sdylewski/MajorHack-Stealthchanger/Nudge Sexbolt Bed Top Mount/Images/bracket_2020mount1.jpg

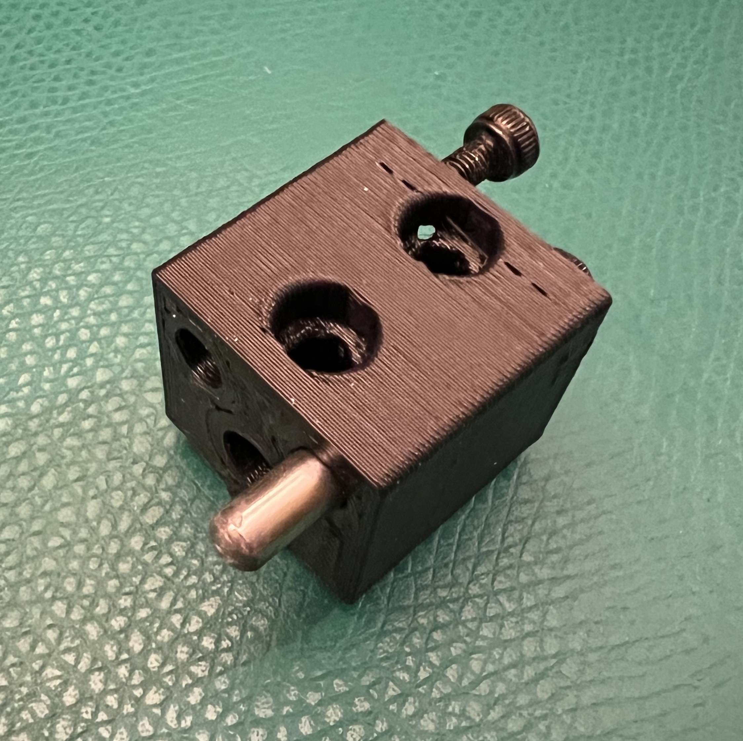
Nudge Sexbolt Bed Top Mount/Images/bracket_2020mount1.jpg
