sdylewski/MajorHack-Stealthchanger/Nudge Sexbolt Bed Top Mount/Images/bracket_2020mount_tnuts.jpg

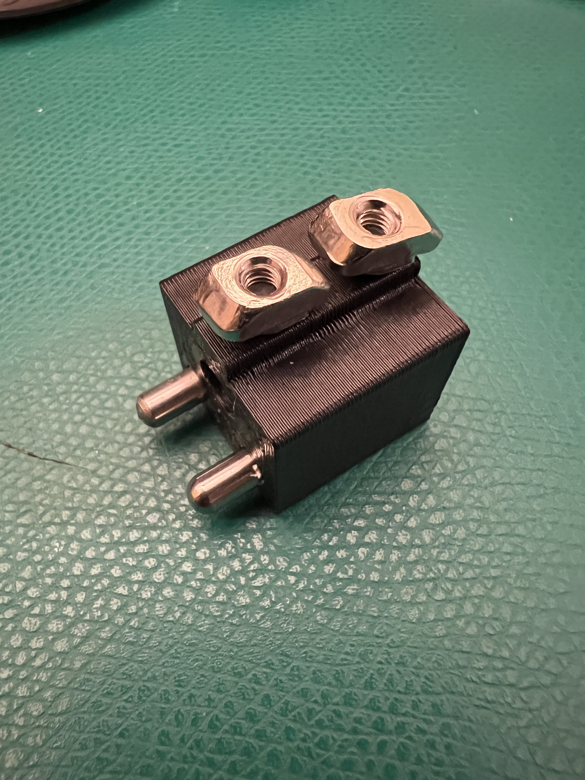
Nudge Sexbolt Bed Top Mount/Images/bracket_2020mount_tnuts.jpg
