sdylewski/MajorHack-Stealthchanger/Nudge Sexbolt Bed Top Mount/Images/bracket_block_heatset.jpg

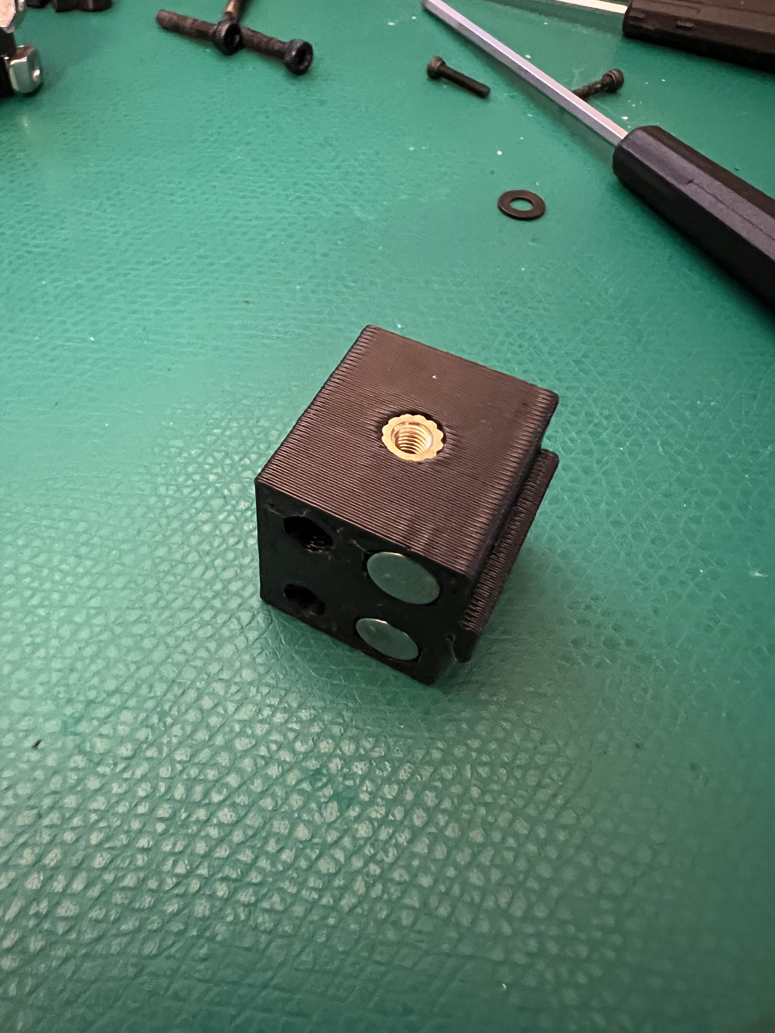
Nudge Sexbolt Bed Top Mount/Images/bracket_block_heatset.jpg
