sdylewski/MajorHack-Stealthchanger/Nudge Sexbolt Bed Top Mount/Images/bracket_magnets.jpg

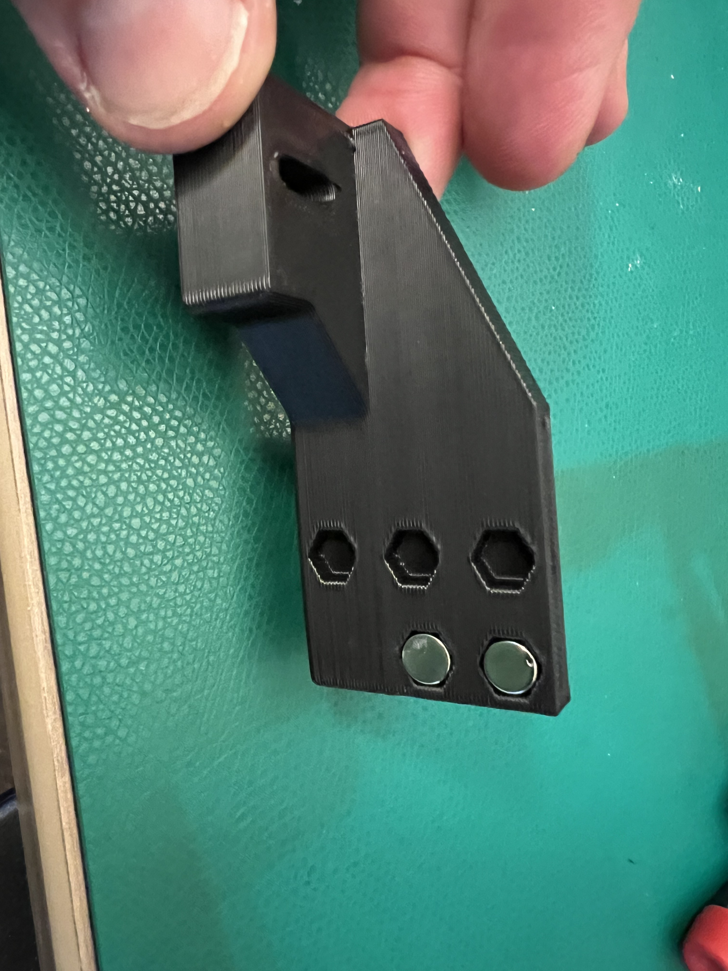
Nudge Sexbolt Bed Top Mount/Images/bracket_magnets.jpg
