sdylewski/MajorHack-Stealthchanger/Nudge Sexbolt Bed Top Mount/Images/bracket_rear_magnets.jpg

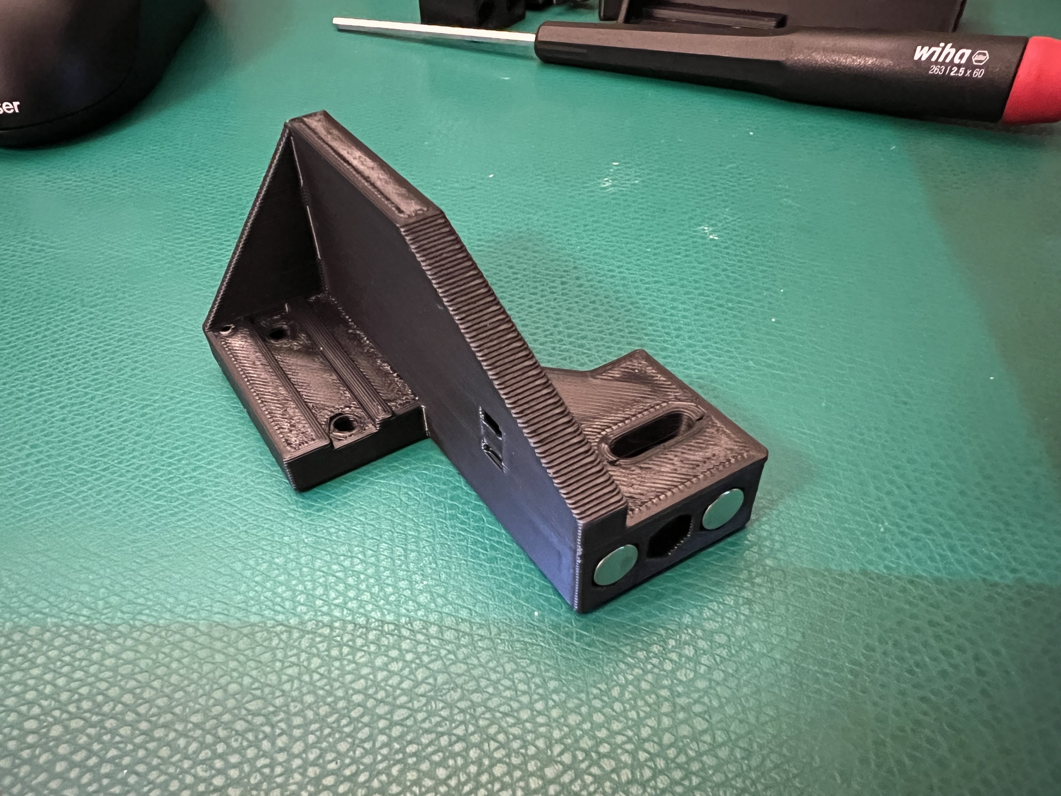
Nudge Sexbolt Bed Top Mount/Images/bracket_rear_magnets.jpg
