sdylewski/MajorHack-Stealthchanger/Nudge Sexbolt Bed Top Mount/Images/in_use.jpg

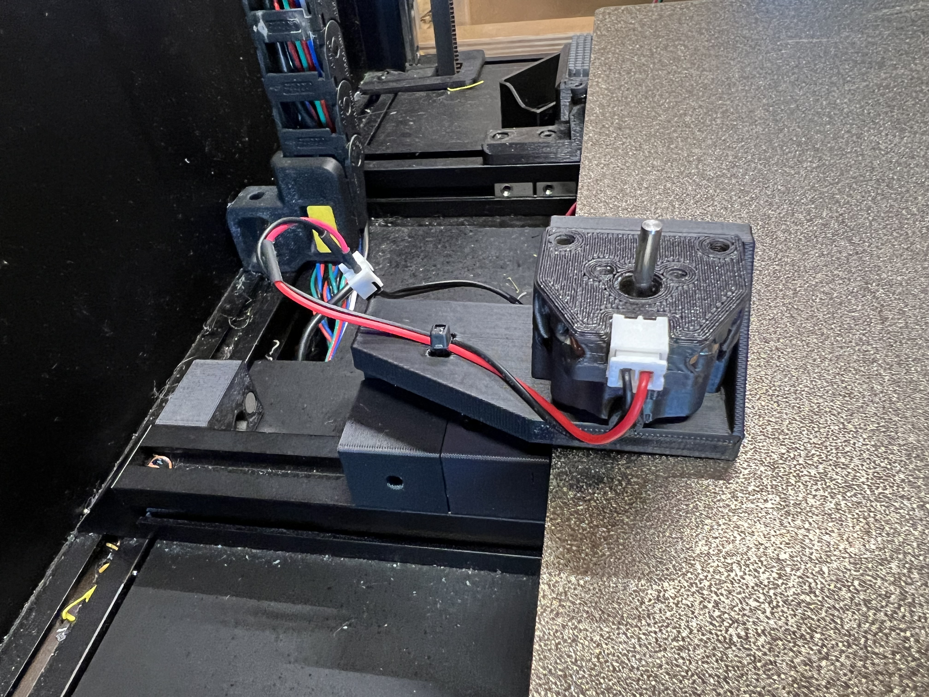
Nudge Sexbolt Bed Top Mount/Images/in_use.jpg
