sdylewski/MajorHack-Stealthchanger/Nudge Sexbolt Bed Top Mount/Images/in_use.png

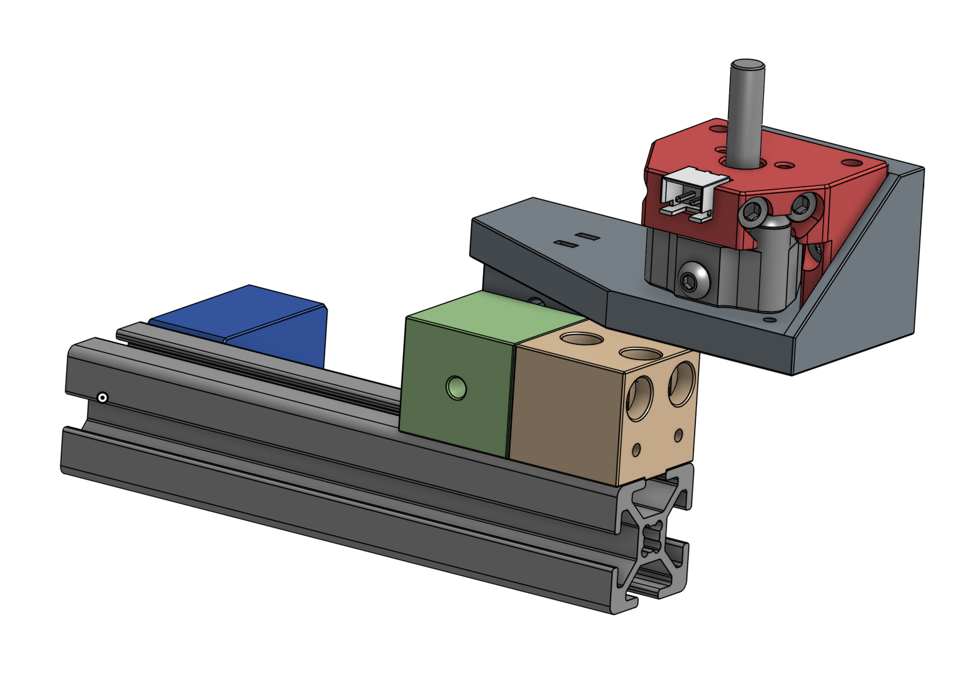
Nudge Sexbolt Bed Top Mount/Images/in_use.png
