sdylewski/MajorHack-Stealthchanger/Nudge Sexbolt Bed Top Mount/Images/rear dock magnets.jpg

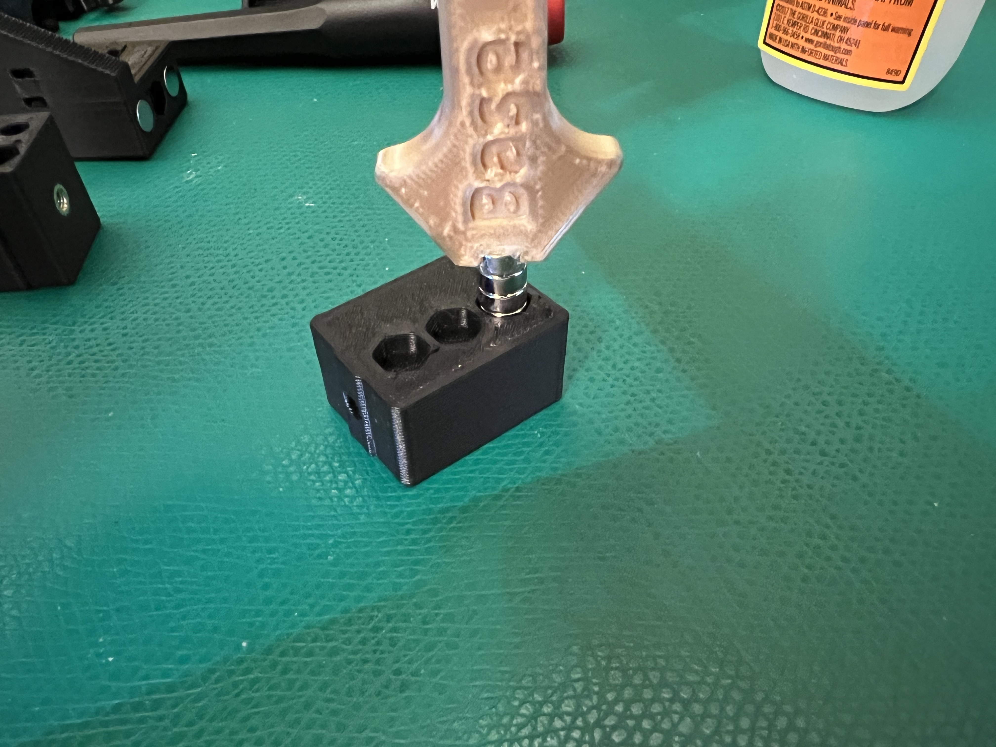
Nudge Sexbolt Bed Top Mount/Images/rear dock magnets.jpg
