sdylewski/MajorHack-Stealthchanger/Nudge Sexbolt Bed Top Mount/Images/Screenshot 2025-10-11 at 2.33.38 PM.png

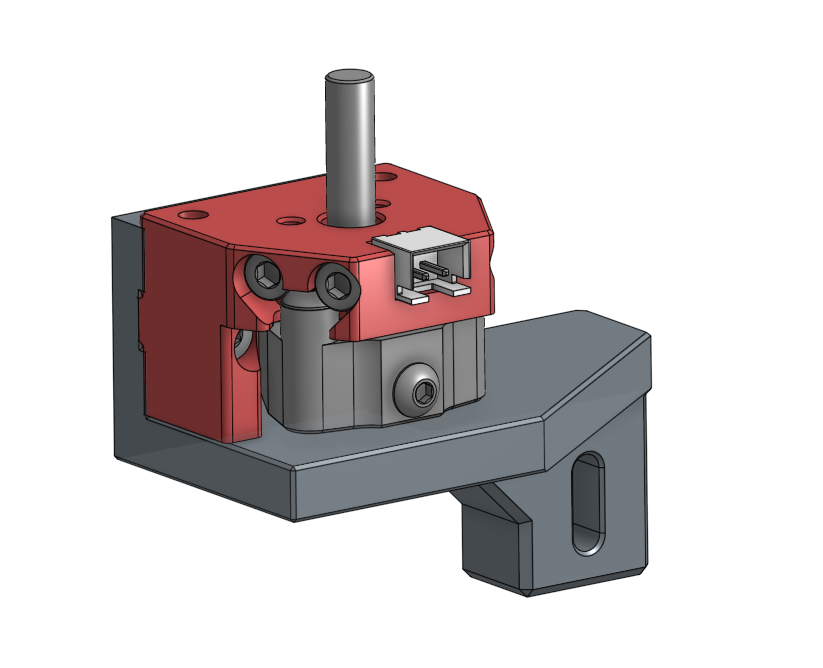
Nudge Sexbolt Bed Top Mount/Images/Screenshot 2025-10-11 at 2.33.38 PM.png
