sdylewski/MajorHack-Stealthchanger/Nudge Sexbolt Bed Top Mount/Images/Screenshot 2025-10-13 at 6.08.04 AM.png

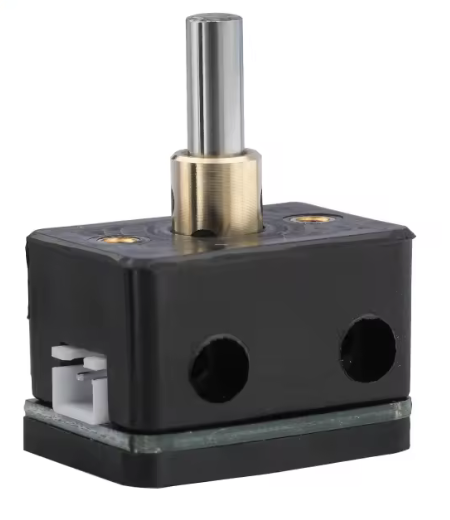
Nudge Sexbolt Bed Top Mount/Images/Screenshot 2025-10-13 at 6.08.04 AM.png
