sdylewski/MajorHack-Stealthchanger/Nudge Sexbolt Bed Top Mount/Images/bracket_block_assembled.jpg

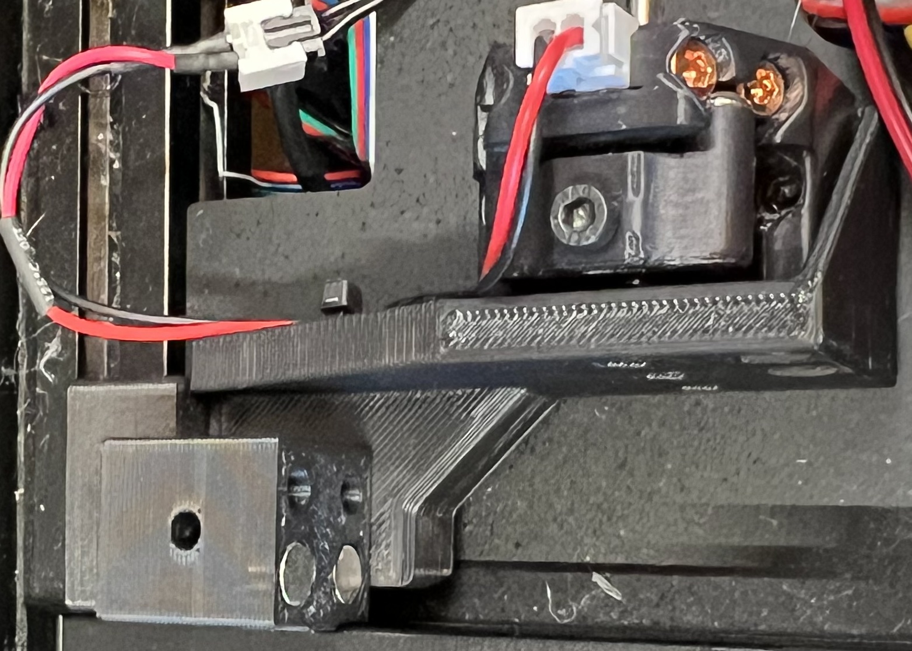
Nudge Sexbolt Bed Top Mount/Images/bracket_block_assembled.jpg
