sdylewski/MajorHack-Stealthchanger/Nudge Sexbolt Bed Top Mount/Images/bracket 2020 mount.jpg

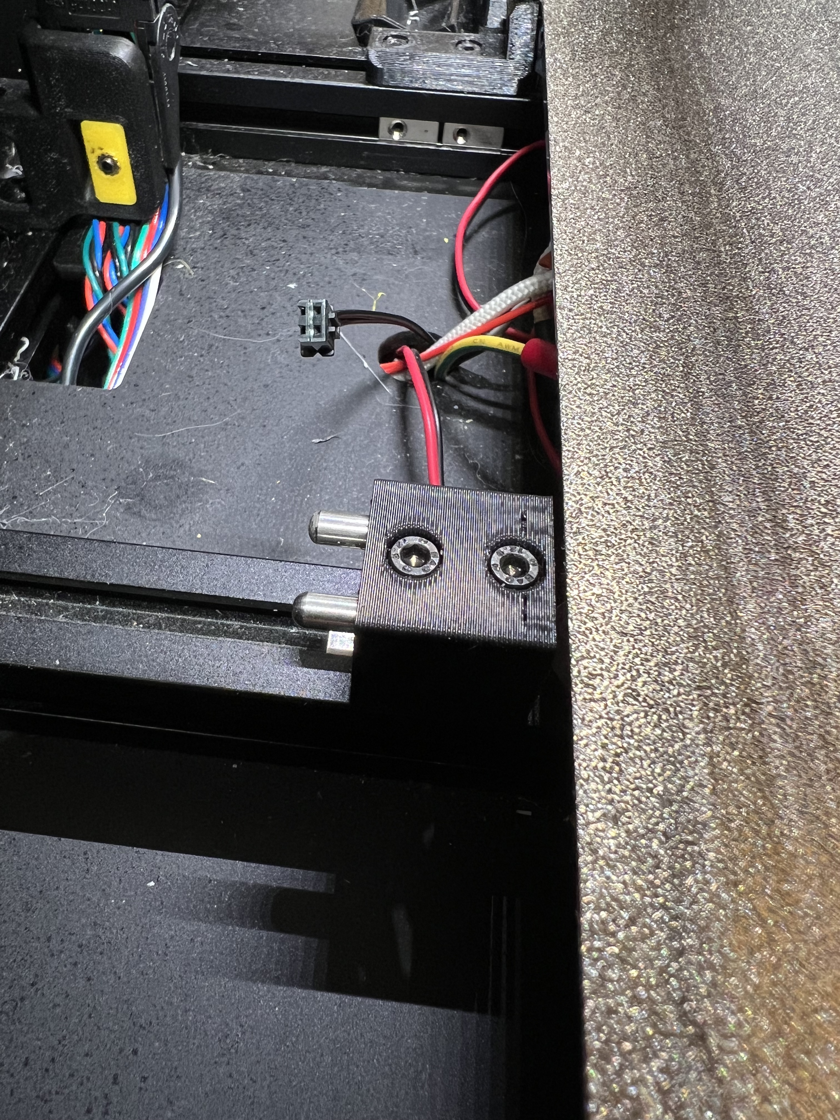
Nudge Sexbolt Bed Top Mount/Images/bracket 2020 mount.jpg
